Nonuwastaken/GBA_Console/CAD Files/Pictures/Front.png

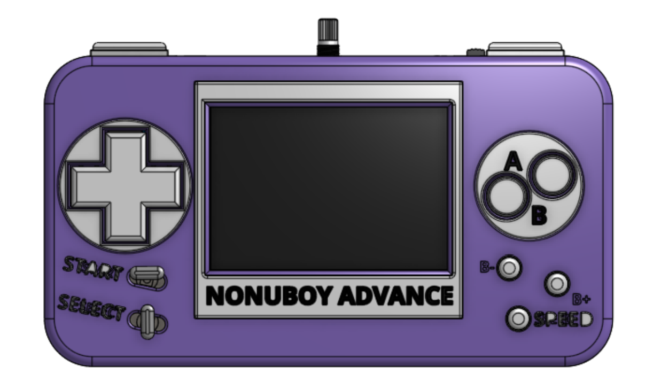
CAD Files/Pictures/Front.png
