Nonuwastaken/GBA_Console/CAD Files/Pictures/Top.png

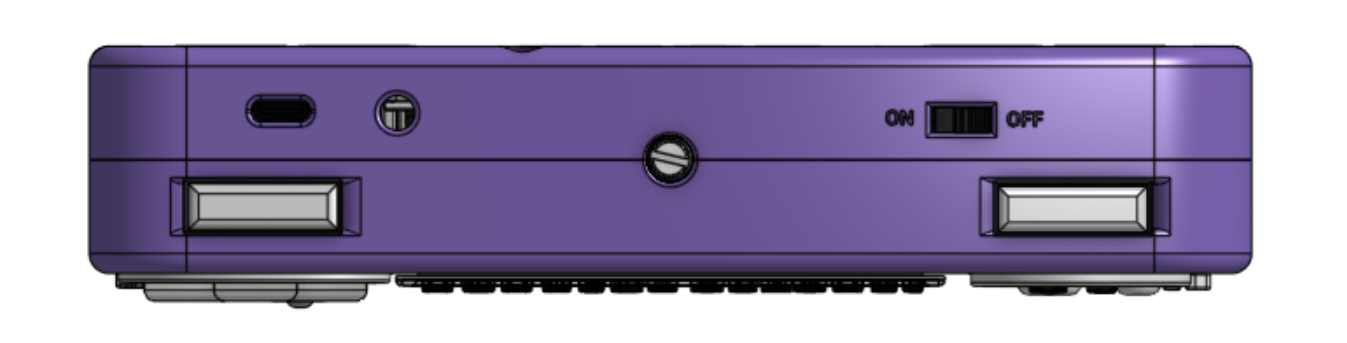
CAD Files/Pictures/Top.png
