Nonuwastaken/GBA_Console/Final_Look/Inside_Look.jpeg

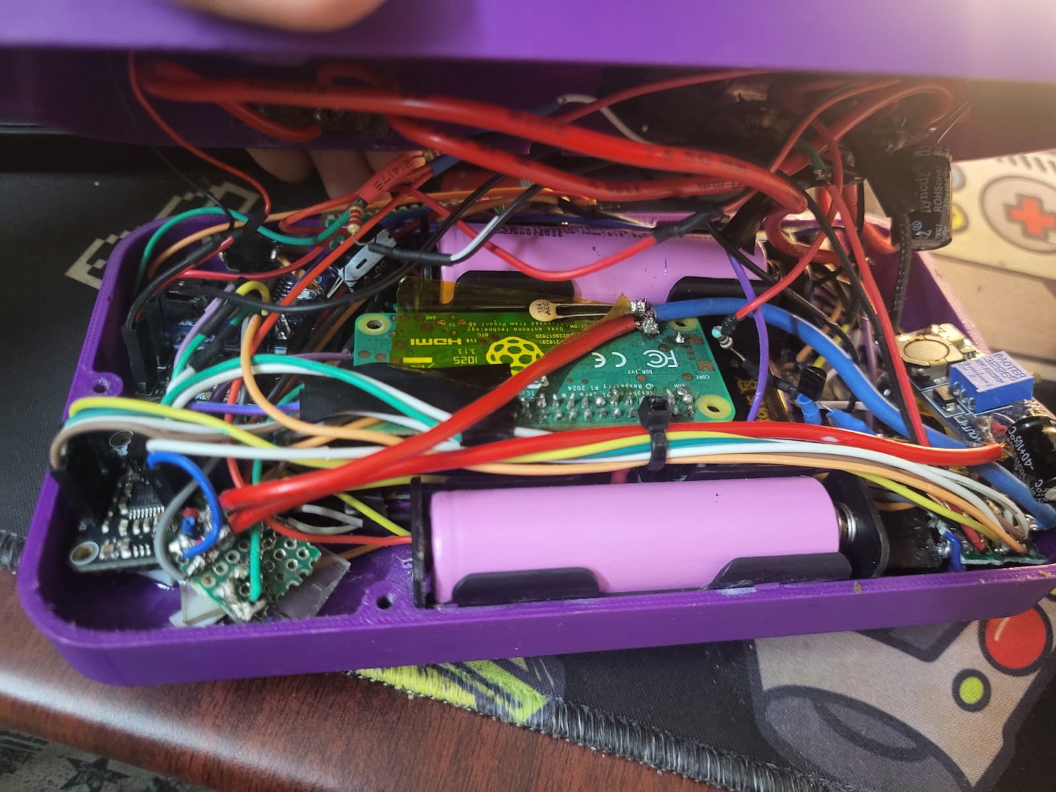
Final_Look/Inside_Look.jpeg
